alexdesaint/TER/Rapport/photoHugo/image003.png

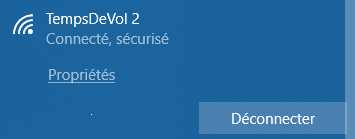
Rapport/photoHugo/image003.png
